farazaleboyeh/led-matrix/src/master.h

#pragma once

#include <WiFiMulti.h>

// const int latchp = 15;
// const int clockp = 17;
// const int datap = 7;

const int latchp = 48;
const int clockp = 47;
const int datap = 45;

#include "matrix_control.h"
#include "spotify_access.h"
